Albert24GG/inktime/Images/drills.png

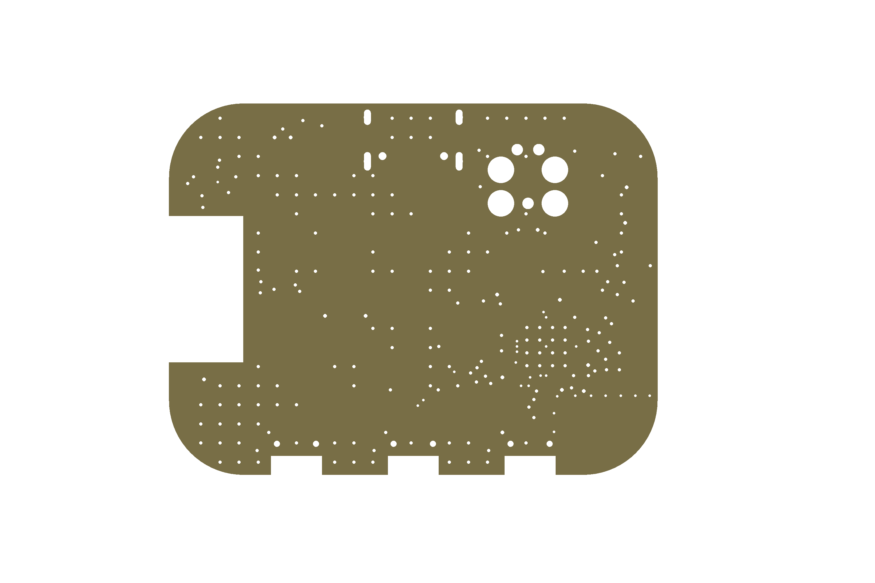
Images/drills.png
