Albert24GG/inktime/Images/assembly_exploded.png

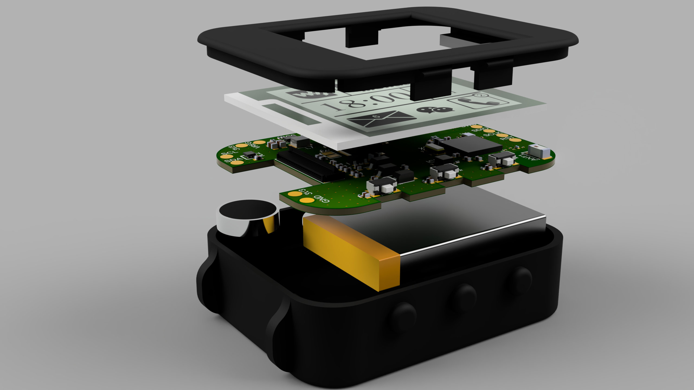
Images/assembly_exploded.png
